linkgo/neurite-sensor-hardware/scr/rc_timer.lua

print("# assign timers")
tmr_com = 0
tmr_com1 = 1
tmr_work = 2
tmr_wifi = 3
tmr_led = 4
tmr_pwr = 5
tmr_but = 6
print("tmr_com: "..tmr_com)
print("tmr_wifi: "..tmr_wifi)
print("tmr_led: "..tmr_led)
print("tmr_pwr: "..tmr_pwr)
print("tmr_but: "..tmr_but)
